SatcomRadio/SWR-Bridge/img/Original/back2.jpg

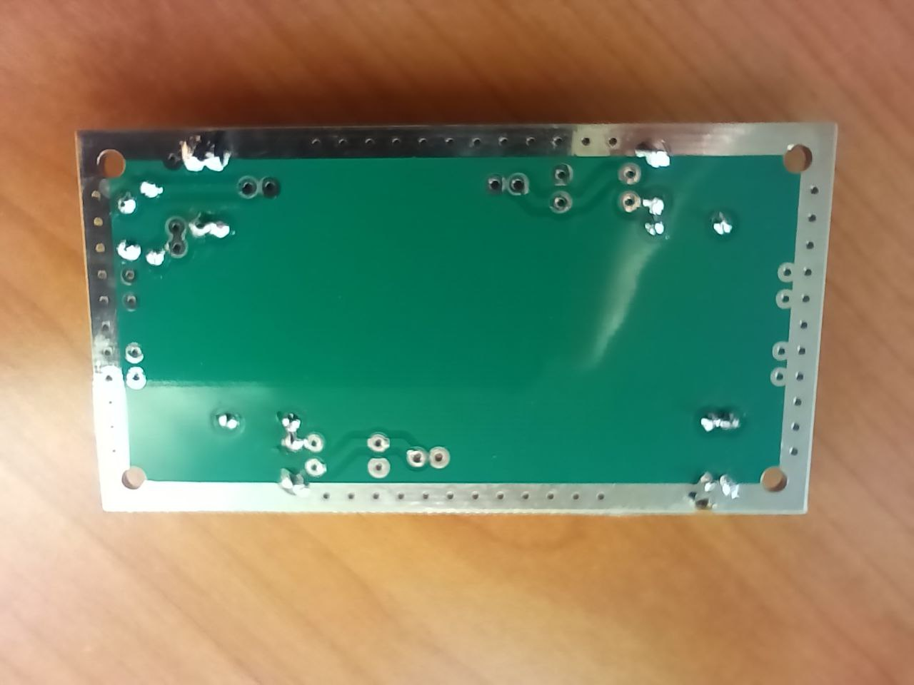
img/Original/back2.jpg
