SatcomRadio/SWR-Bridge/img/Original/det1.jpg

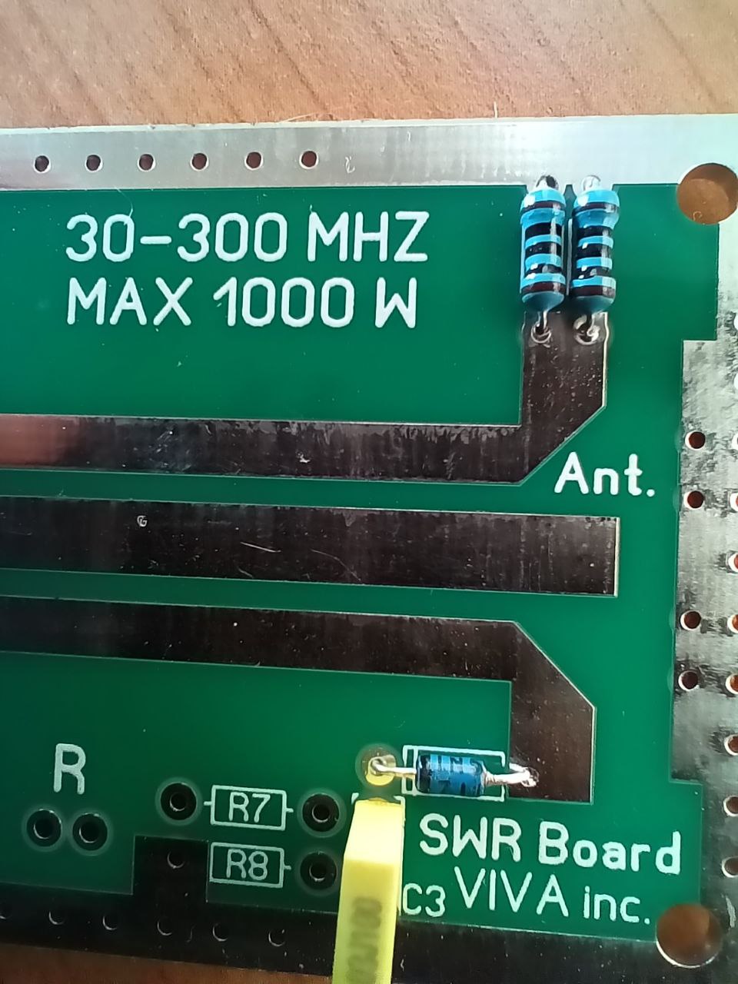
img/Original/det1.jpg
