SatcomRadio/SWR-Bridge/img/Original/manual1.jpg

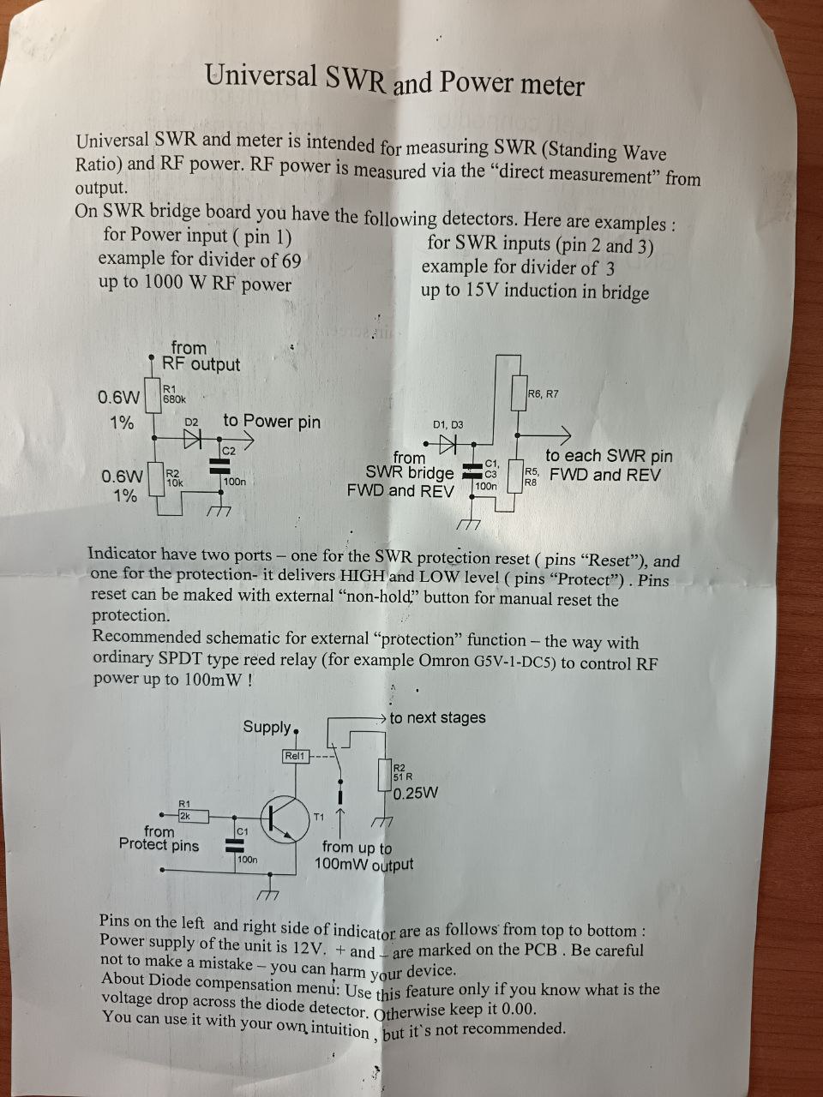
img/Original/manual1.jpg
