SatcomRadio/SWR-Bridge/img/Original/manual2.jpg

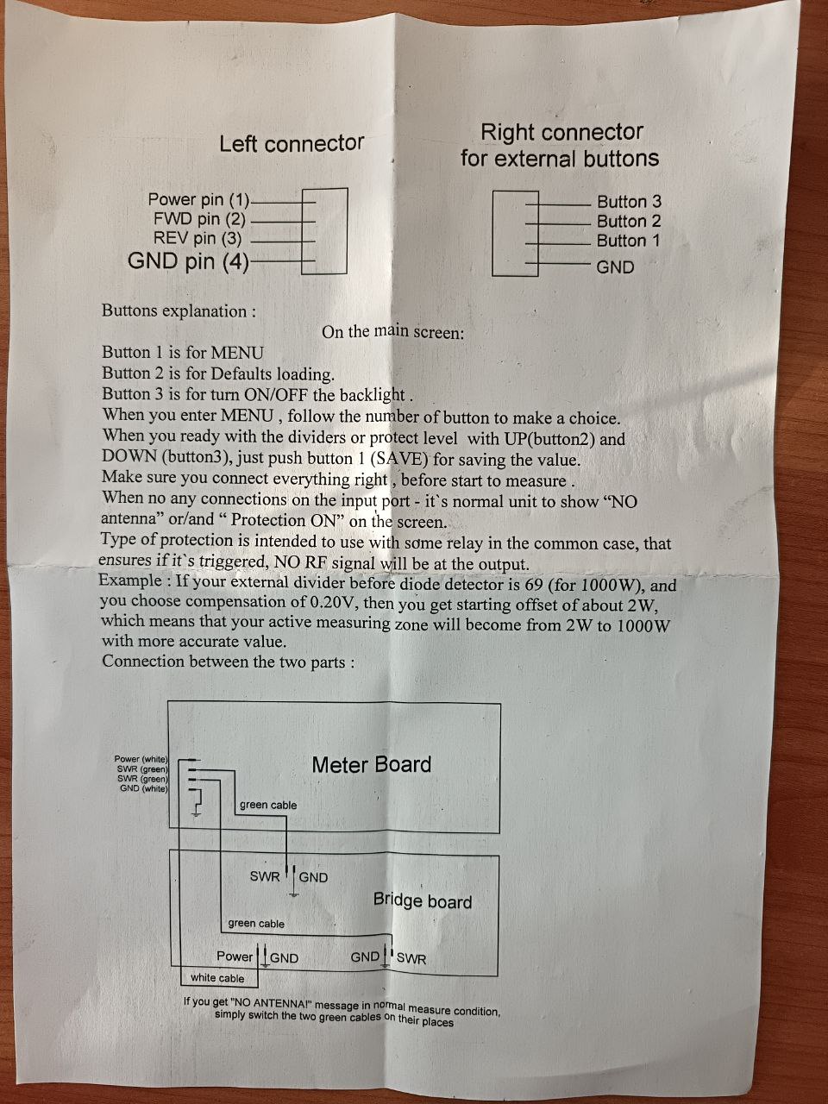
img/Original/manual2.jpg
