SatcomRadio/SWR-Bridge/img/Original/measure2.jpg

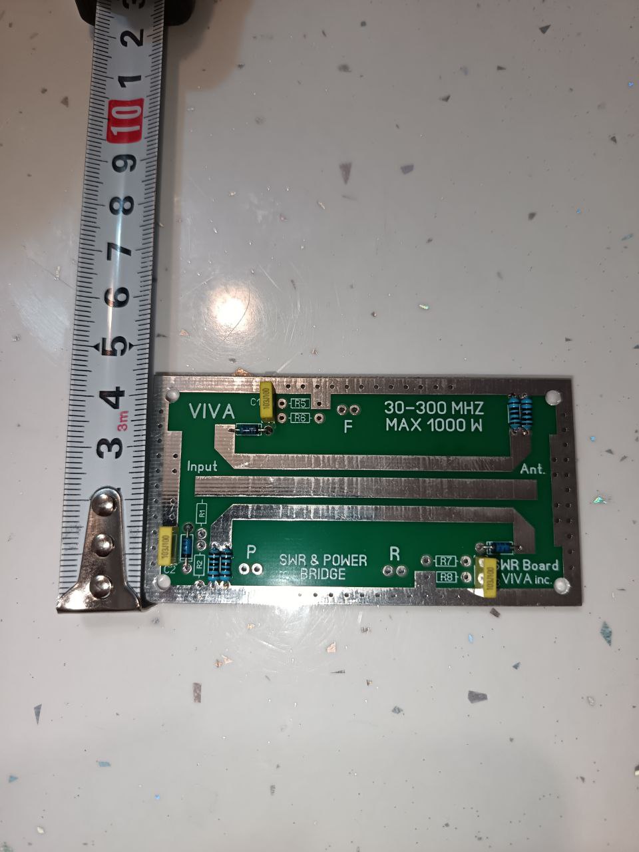
img/Original/measure2.jpg
