SatcomRadio/SWR-Bridge/img/Original/measure.jpg

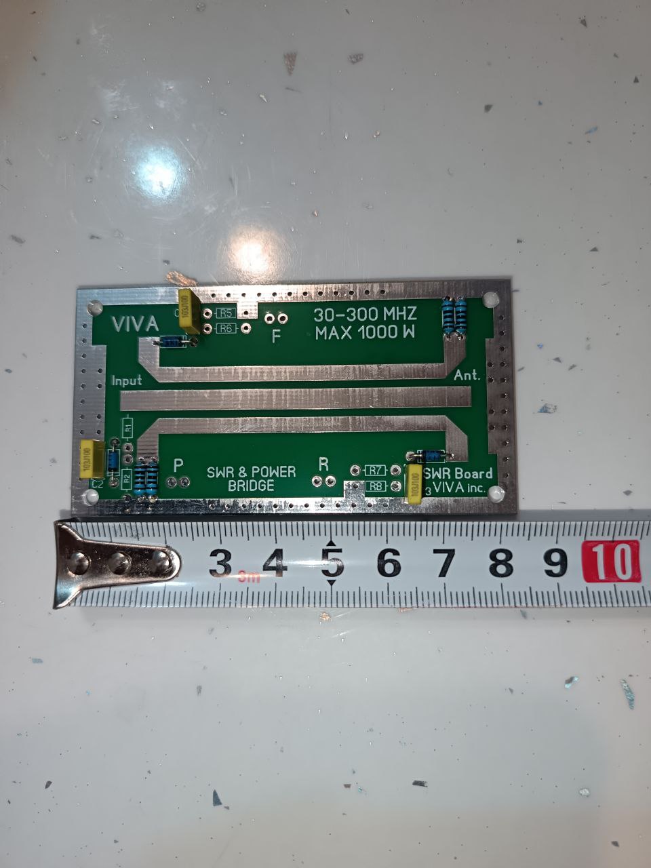
img/Original/measure.jpg
